Board-Folk/TIM011B/Extensions/tim011_video_fix/images/composite.jpg

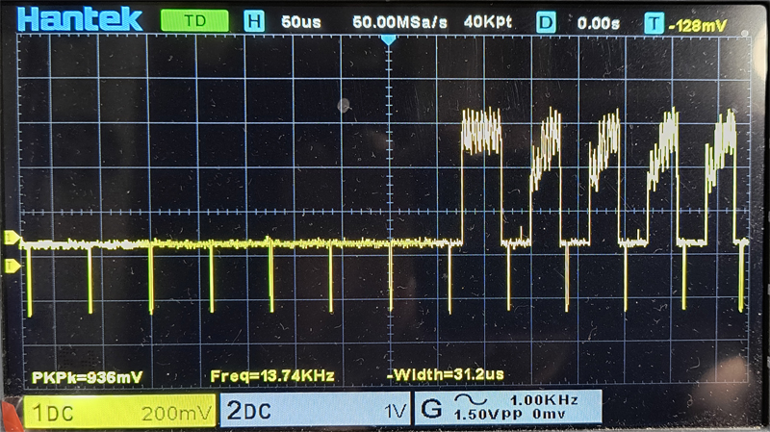
Extensions/tim011_video_fix/images/composite.jpg
