Board-Folk/TIM011B/Extensions/tim011_video_fix/images/hsync.jpg

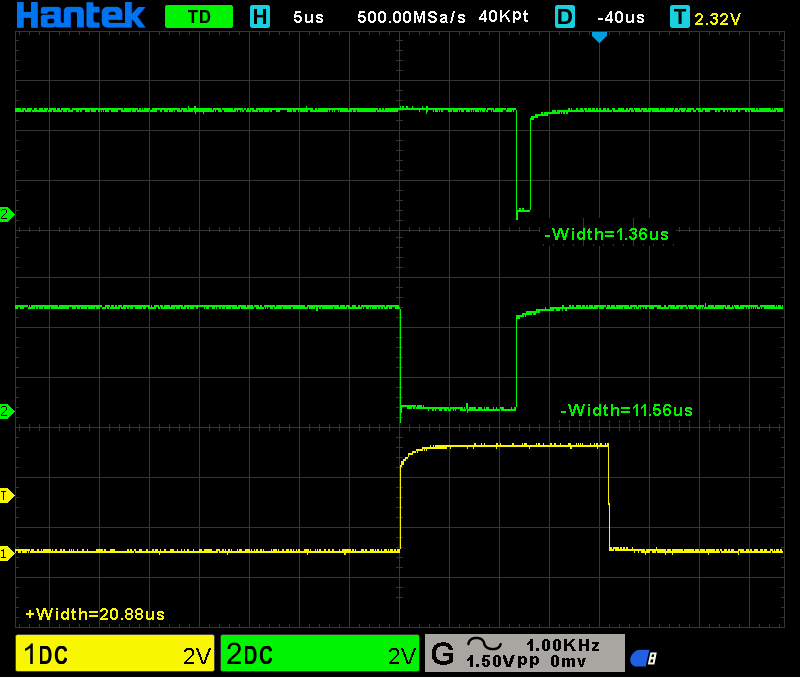
Extensions/tim011_video_fix/images/hsync.jpg
