Board-Folk/TIM011B/Extensions/TIMPS2Key/v2/Arduino/TIMPS2Key/keymap.h

// keymap.h
// @grandoldian 03/2024
// v0.1.1 09/04/2024

// Keyboard mappings courtesy of Marko Šolajić

byte keymap_noshift[256] = {
  0xff, 0xff, 0xff, 0xff, 0xfa, 0xff, 0xff, 0xff,   // 0 - 7
  0xff, 0xff, 0xff, 0xff, 0xff, 0xff, 0x0a, 0xff,   // 8 - 15
  0xff, 0xd0, 0xd2, 0xd1, 0xd3, 0xc4, 0xc3, 0xc1,   // 16 - 23
  0xc2, 0xff, 0x7f, 0x1b, 0x08, 0x09, 0x0d, 0x20,   // 24 - 31
  0xf0, 0xf1, 0xf2, 0xf3, 0xf4, 0xf5, 0xf6, 0xf7,   // 32 - 39
  0xf8, 0xf9, 0xee, 0xcd, 0xec, 0xed, 0xff, 0xff,   // 40 - 47
  0x30, 0x31, 0x32, 0x33, 0x34, 0x35, 0x36, 0x37,   // 48 - 55
  0x38, 0x39, 0xbd, 0x2c, 0x2d, 0x2e, 0x2f, 0xff,   // 56 - 63
  0x80, 0x41, 0x42, 0x43, 0x44, 0x45, 0x46, 0x47,   // 64 - 71
  0x48, 0x49, 0x4a, 0x4b, 0x4c, 0x4d, 0x4e, 0x4f,   // 72 - 79
  0x50, 0x51, 0x52, 0x53, 0x54, 0x55, 0x56, 0x57,   // 80 - 87
  0x58, 0x59, 0x5a, 0xce, 0xc0, 0xcb, 0xcc, 0x2b,   // 88 - 95
  0xff, 0xd4, 0xd5, 0xd6, 0xd7, 0xd8, 0xd9, 0xda,   // 96 - 103
  0xdb, 0xdc, 0xdd, 0xde, 0xff, 0xff, 0xff, 0xff,   // 104 - 111
  0xff, 0xff, 0xff, 0xff, 0xff, 0xff, 0xff, 0xff,   // 112 - 119
  0xff, 0xff, 0xff, 0xff, 0xff, 0xff, 0xff, 0xff,   // 120 - 127
  0xff, 0xff, 0xff, 0xff, 0xff, 0xff, 0xff, 0xff,   // 128 - 135
  0xff, 0xff, 0xff, 0x3c, 0xff, 0xff, 0xff, 0xff,   // 136 - 143
  0xff, 0xff, 0xff, 0xff, 0xff, 0xff, 0xff, 0xff,   // 144 - 151
  0xff, 0xff, 0xff, 0xff, 0xff, 0xff, 0xff, 0xff,   // 152 - 159
  0xff, 0xff, 0xff, 0xff, 0xff, 0xff, 0xff, 0xff,   // 160 - 167
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
  0xff, 0xff, 0xff, 0xff, 0xff, 0xff, 0xff, 0xff,   // 224 - 231
  0xff, 0xff, 0xff, 0xff, 0xff, 0xff, 0xff, 0xff,   // 232 - 239
  0xff, 0xff, 0xff, 0xff, 0xff, 0xff, 0xff, 0xff,   // 240 - 247
  0xff, 0xff, 0xff, 0xff, 0xff, 0xff, 0xff, 0xff    // 248 - 255
};
